MakerBogans/Fourbie/Fourbie v2/STL/XY Joints/v27 - Left XY Joint - Bottom.stl

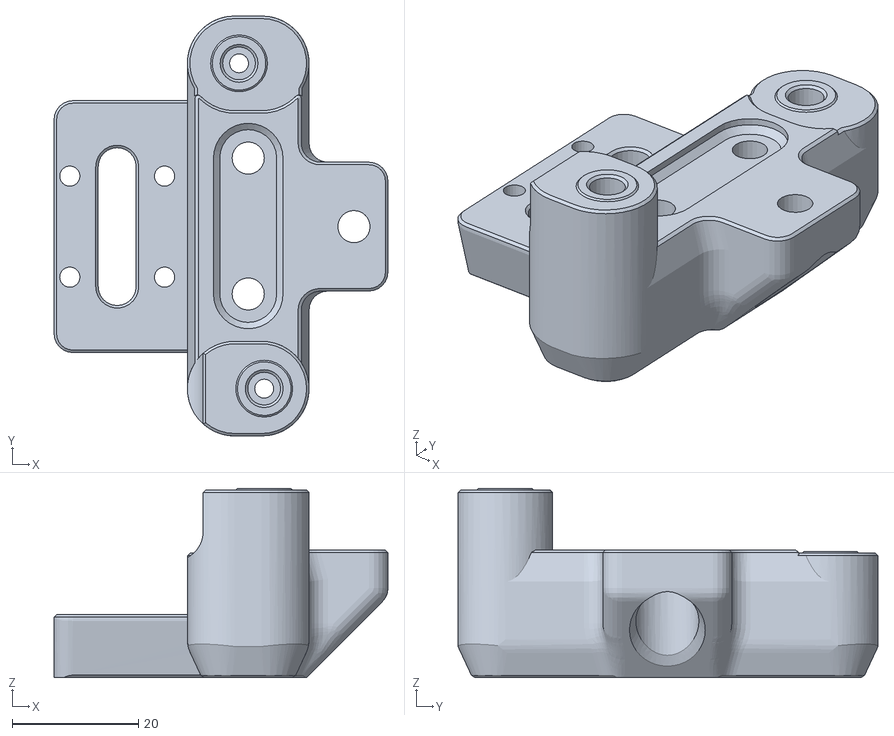
[picture p24: CAD file, 2023-07-19]
Fourbie v2/STL/XY Joints/v27 - Left XY Joint - Bottom.stl
52.9 x 66.5 x 30.0
