MakerBogans/Fourbie/Fourbie v2/Mods/Killajoedotcom/AB Drives for Trident/Front AB Drives/4 Inch Lift/Thicker Front Left_Fourbie v2_Tensioner Frame_x2.stl

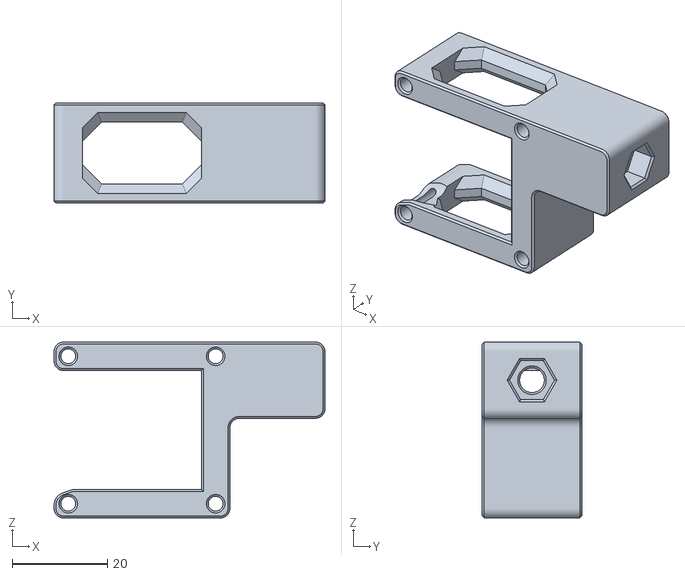
[picture p25: CAD file, 2024-02-14]
Fourbie v2/Mods/Killajoedotcom/AB Drives for Trident/Front AB Drives/4 Inch Lift/Thicker Front Left_Fourbie v2_Tensioner Frame_x2.stl
57.0 x 21.0 x 37.0
