MakerBogans/Fourbie/Fourbie v2/Mods/Killajoedotcom/AB Drives for Trident/Rear AB Drives/Rear AB - Right - Tensioner Frame.stl

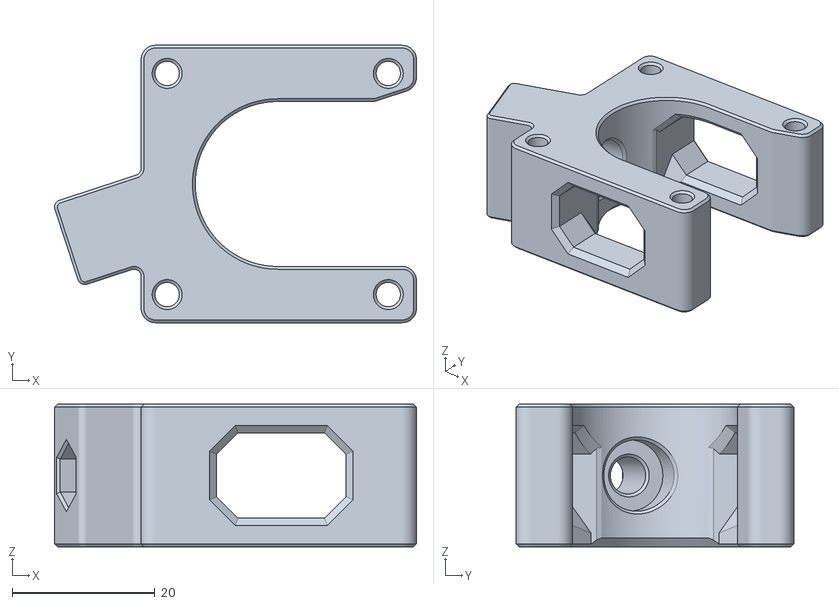
[picture p26: CAD file, 2024-02-14]
Fourbie v2/Mods/Killajoedotcom/AB Drives for Trident/Rear AB Drives/Rear AB - Right - Tensioner Frame.stl
50.7 x 38.9 x 20.0
