MakerBogans/Fourbie/Fourbie v2/Mods/Verethy/Eureaka Probe Dock/Goliath_short_wider_Eureka.3mf

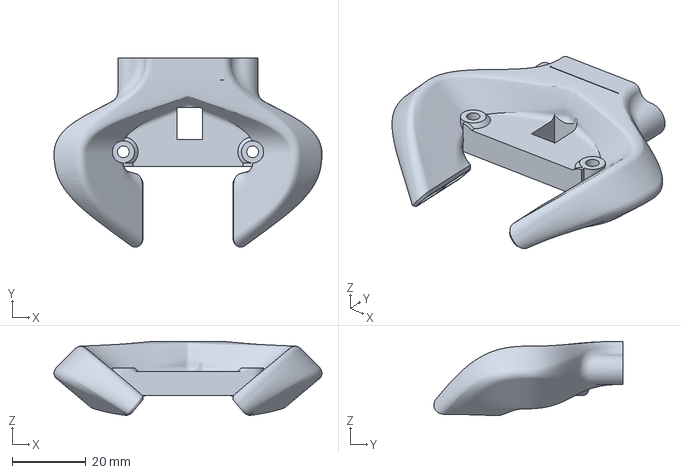
[picture p27: CAD file, 2023-07-19]
Fourbie v2/Mods/Verethy/Eureaka Probe Dock/Goliath_short_wider_Eureka.3mf
72.6 x 51.1 x 20.1 mm
