MakerBogans/Fourbie/Fourbie v2/STL/Cable Tie Mounts/Cable Tie Mount - Wider Base.stl

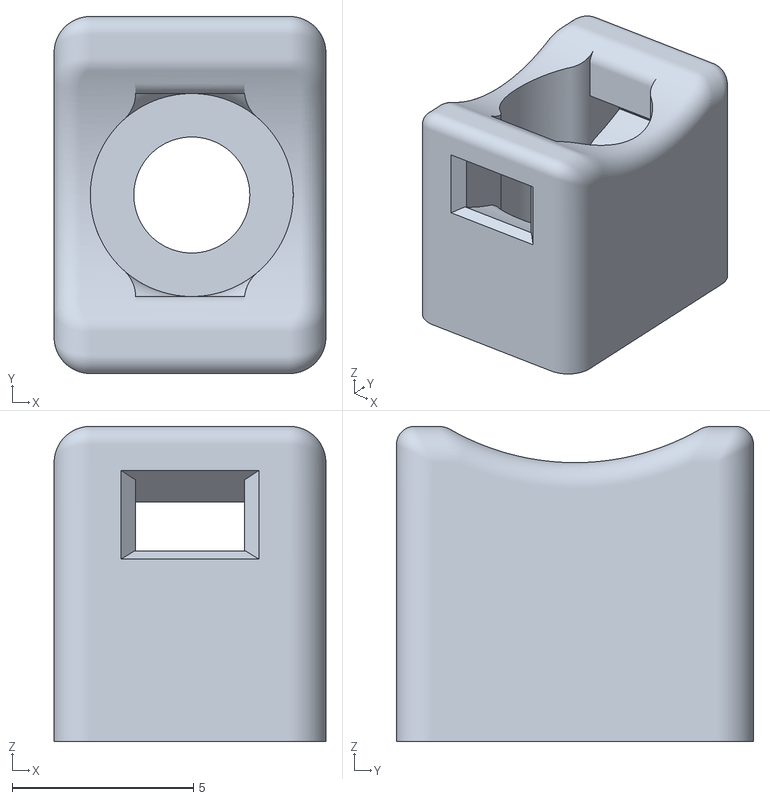
[picture p28: CAD file, 2023-06-04]
Fourbie v2/STL/Cable Tie Mounts/Cable Tie Mount - Wider Base.stl
7.50 x 9.85 x 8.70
