MakerBogans/Fourbie/Fourbie v2/STL/Toolhead/Alternative front belt clamps/Toothed Belt Clamp - Rear- x2 -Print Solid!.stl

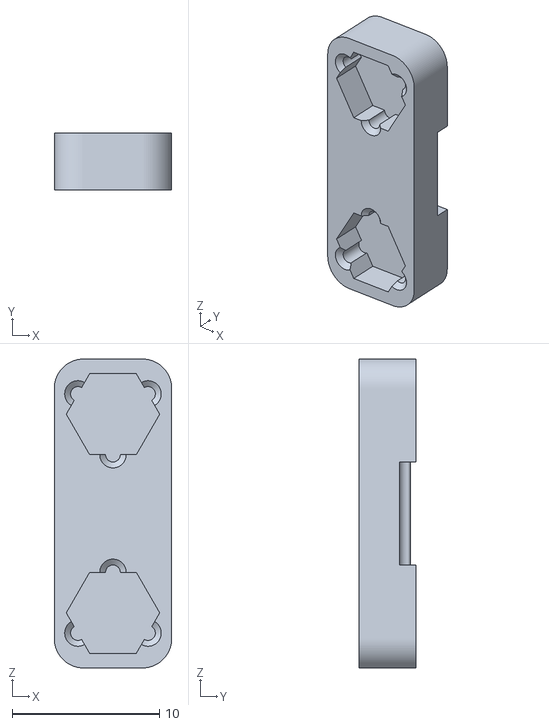
[picture p29: CAD file, 2023-06-04]
Fourbie v2/STL/Toolhead/Alternative front belt clamps/Toothed Belt Clamp - Rear- x2 -Print Solid!.stl
7.98 x 3.90 x 21.0
