MakerBogans/Fourbie/Fourbie v2/STL/Toolhead/VZBot Toolhead Mods/MGN9/Top plate MGN9H Sherpa Micro.stl

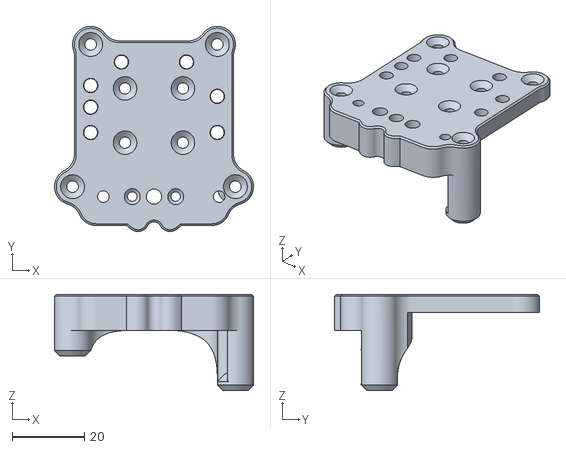
[picture p30: CAD file, 2023-06-04]
Fourbie v2/STL/Toolhead/VZBot Toolhead Mods/MGN9/Top plate MGN9H Sherpa Micro.stl
55.0 x 56.7 x 26.6
