MakerBogans/Fourbie/Fourbie v2/STL/Toolhead/VZBot Toolhead Mods/Stubby Back Plate - No Mast.stl

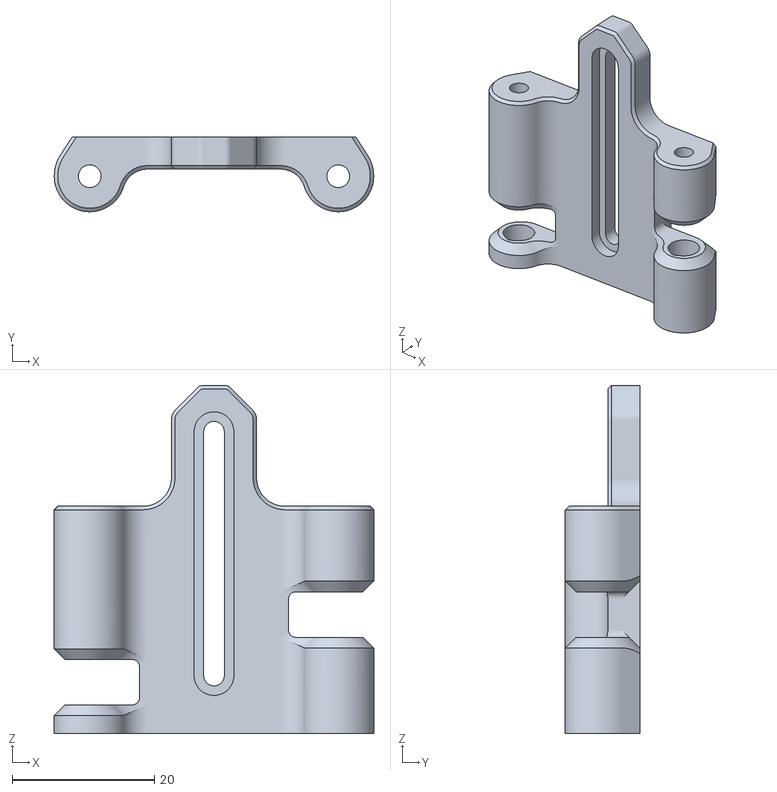
[picture p31: CAD file, 2023-06-04]
Fourbie v2/STL/Toolhead/VZBot Toolhead Mods/Stubby Back Plate - No Mast.stl
45.0 x 10.5 x 49.0
