MakerBogans/Fourbie/Fourbie v2/STL/Tools/CF Tube Drill Guild MGN12 End hole.stl

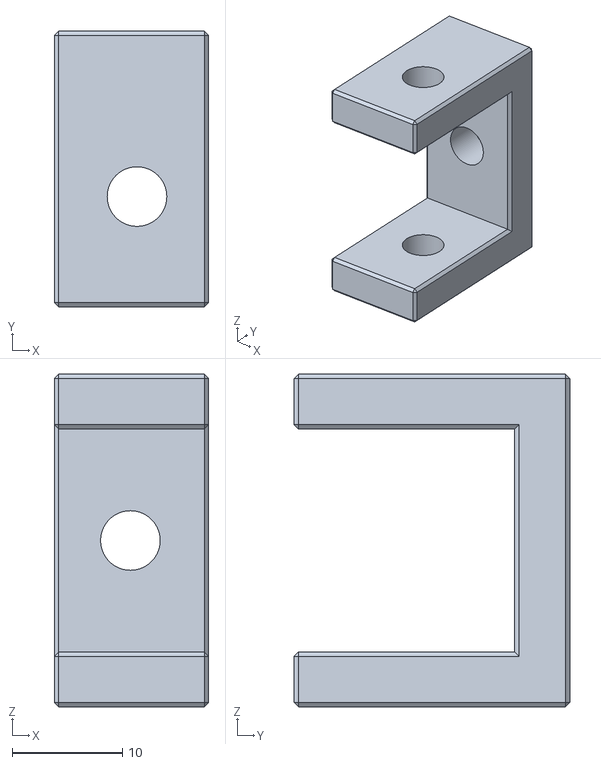
[picture p32: CAD file, 2023-06-04]
Fourbie v2/STL/Tools/CF Tube Drill Guild MGN12 End hole.stl
14.0 x 25.0 x 30.2
