MakerBogans/Fourbie/Fourbie v2/STL/XY Joints/MGN12/MGN12 XY Joints - Left - Bottom.stl

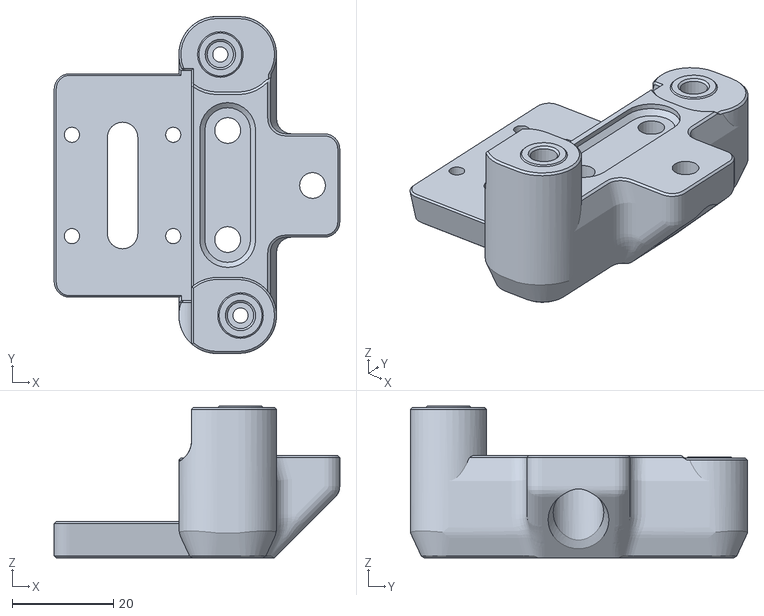
[picture p33: CAD file, 2023-07-19]
Fourbie v2/STL/XY Joints/MGN12/MGN12 XY Joints - Left - Bottom.stl
56.4 x 66.5 x 30.0
