MakerBogans/Fourbie/Fourbie v2/Mods/Killajoedotcom/AB Drives for Trident/Front AB Drives/4 Inch Lift/Thicker Front Left_Fourbie v2_Top.stl

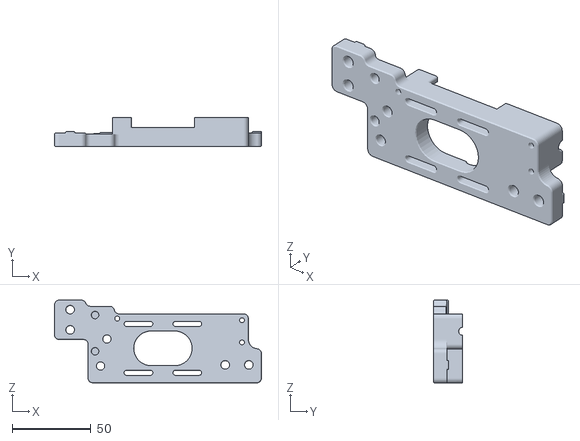
[picture p35: CAD file, 2024-02-14]
Fourbie v2/Mods/Killajoedotcom/AB Drives for Trident/Front AB Drives/4 Inch Lift/Thicker Front Left_Fourbie v2_Top.stl
131.4 x 18.6 x 52.5
