MakerBogans/Fourbie/Fourbie v2/Mods/Killajoedotcom/AB Drives for Trident/Front AB Drives/Knurled Knob_x2.3mf

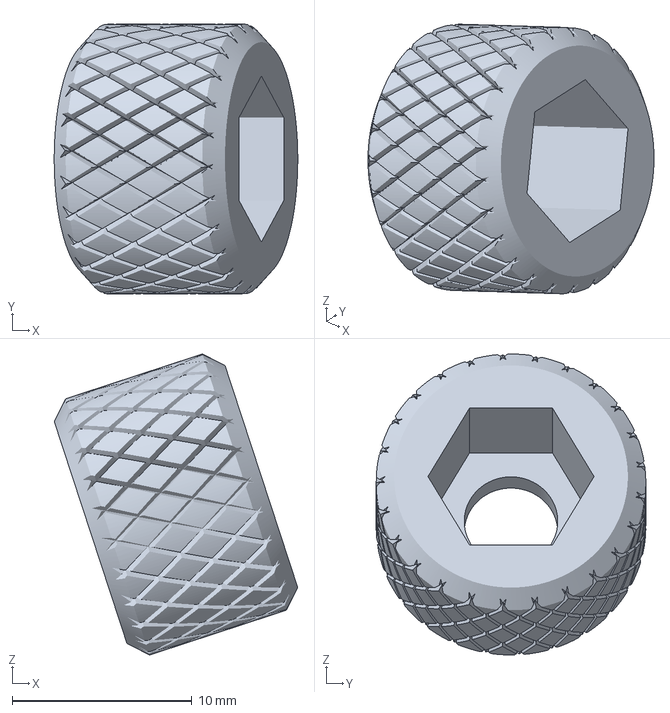
[picture p36: CAD file, 2024-02-14]
Fourbie v2/Mods/Killajoedotcom/AB Drives for Trident/Front AB Drives/Knurled Knob_x2.3mf
13.6 x 15.0 x 16.7 mm
