MakerBogans/Fourbie/Fourbie v2/STL/AB/v26 - Rear Right - Bottom.stl

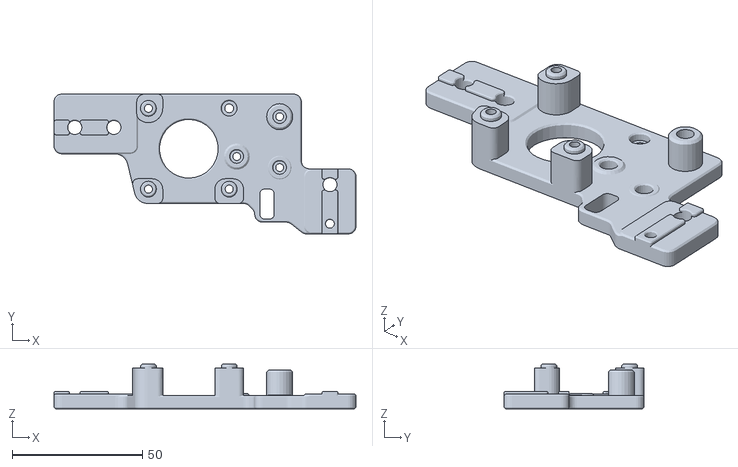
[picture p37: CAD file, 2023-07-19]
Fourbie v2/STL/AB/v26 - Rear Right - Bottom.stl
115.9 x 53.7 x 17.1
