MakerBogans/Fourbie/Fourbie v2/STL/Cable Tie Mounts/Cable Tie Mount - Flat top wide base.stl

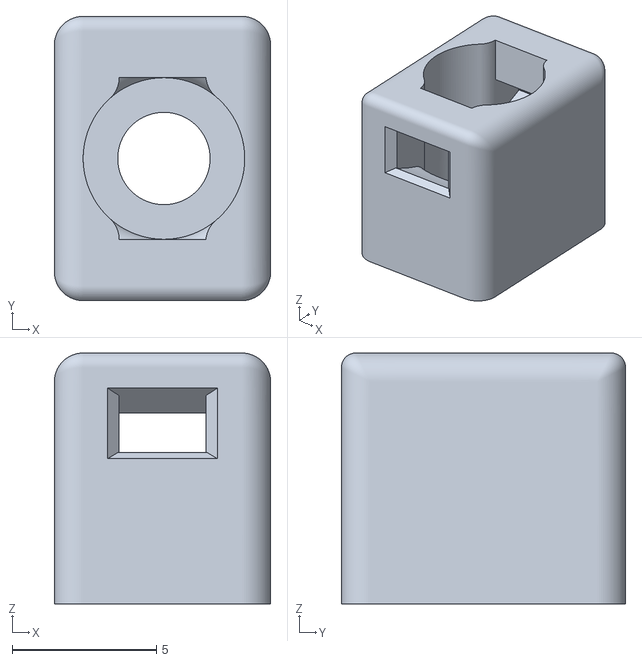
[picture p38: CAD file, 2023-06-04]
Fourbie v2/STL/Cable Tie Mounts/Cable Tie Mount - Flat top wide base.stl
7.50 x 9.85 x 8.70
