MakerBogans/Fourbie/Fourbie v2/STL/Toolhead/VZBot Toolhead Mods/LGX Lite Side Cable Holder.stl

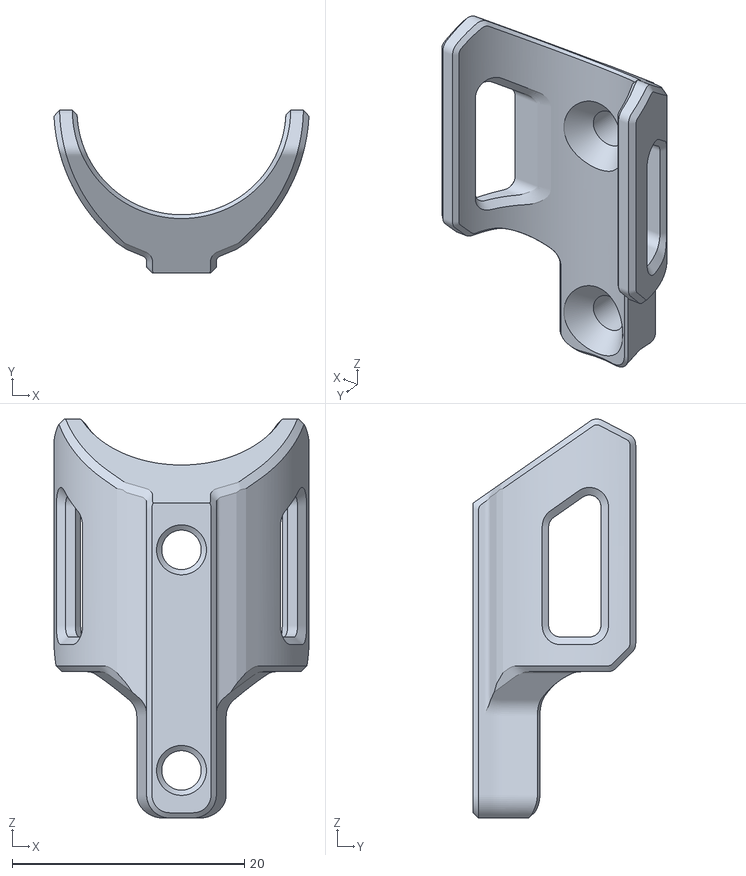
[picture p39: CAD file, 2023-06-04]
Fourbie v2/STL/Toolhead/VZBot Toolhead Mods/LGX Lite Side Cable Holder.stl
22.0 x 14.0 x 34.4
