MakerBogans/Fourbie/Fourbie v2/STL/Tools/CF Tube Drill Guide MGN9 Rail Retainer.stl

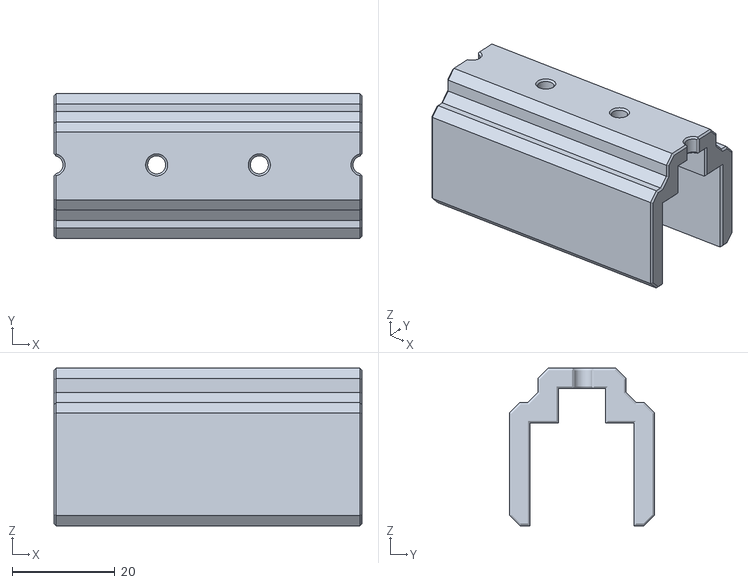
[picture p40: CAD file, 2023-06-04]
Fourbie v2/STL/Tools/CF Tube Drill Guide MGN9 Rail Retainer.stl
60.0 x 28.2 x 30.7
