MakerBogans/Fourbie/Fourbie v2/STL/XY Joints/MGN12/MGN12 XY Joints - Right - Top.stl

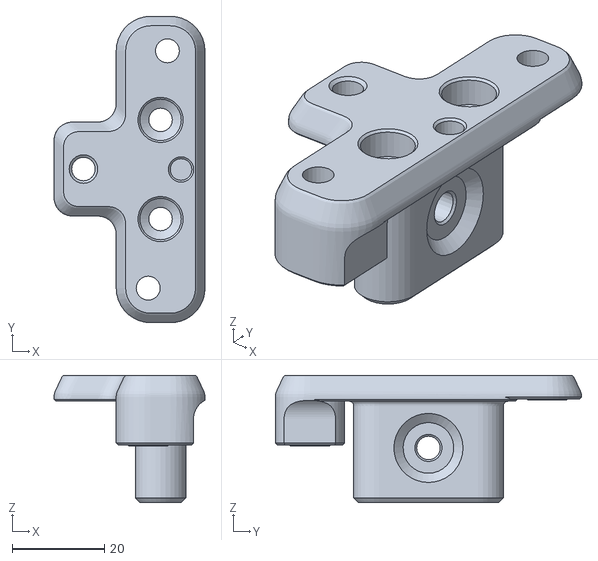
[picture p41: CAD file, 2023-07-19]
Fourbie v2/STL/XY Joints/MGN12/MGN12 XY Joints - Right - Top.stl
32.8 x 66.5 x 27.6
