MakerBogans/Fourbie/Fourbie v2/Mods/Killajoedotcom/AB Drives for Trident/Front AB Drives/Front AB - Right - Top.3mf

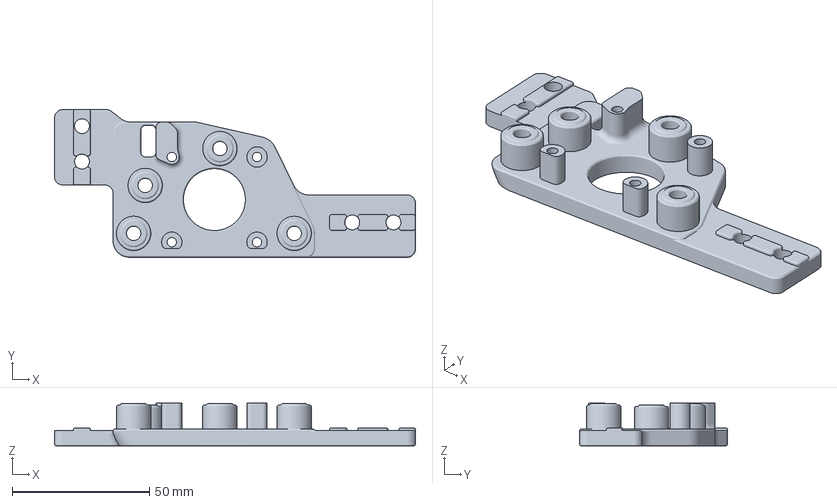
[picture p43: CAD file, 2024-02-14]
Fourbie v2/Mods/Killajoedotcom/AB Drives for Trident/Front AB Drives/Front AB - Right - Top.3mf
131.3 x 53.7 x 15.6 mm
