MakerBogans/Fourbie/Fourbie v2/Mods/Killajoedotcom/AB Drives for Trident/Rear AB Drives/Knob - Basic.stl

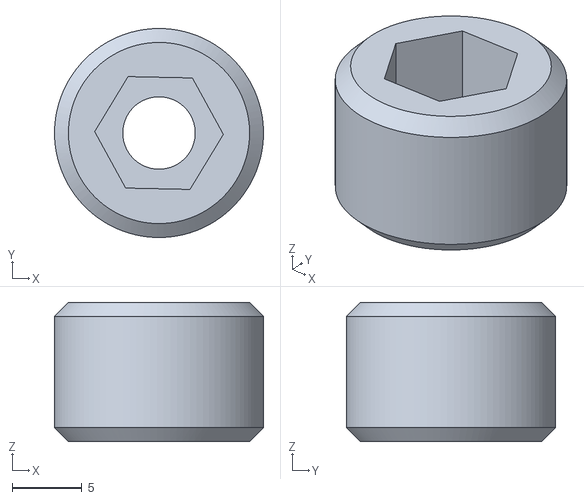
[picture p44: CAD file, 2024-02-14]
Fourbie v2/Mods/Killajoedotcom/AB Drives for Trident/Rear AB Drives/Knob - Basic.stl
15.0 x 15.0 x 10.0
