MakerBogans/Fourbie/Fourbie v2/STL/AB/v26 - Front Right - Top.stl

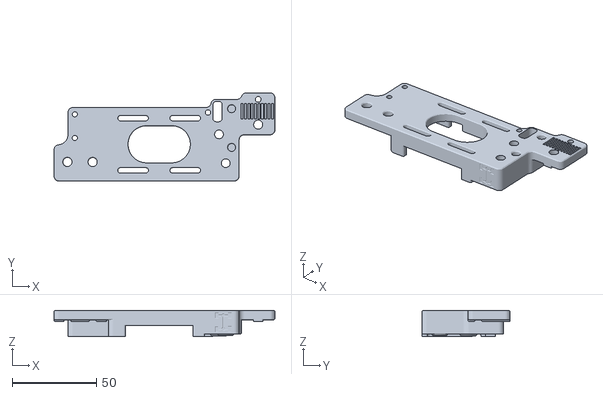
[picture p45: CAD file, 2023-07-19]
Fourbie v2/STL/AB/v26 - Front Right - Top.stl
131.4 x 52.5 x 15.6
