MakerBogans/Fourbie/Fourbie v2/STL/Cable Tie Mounts/Cable Tie Mount.stl

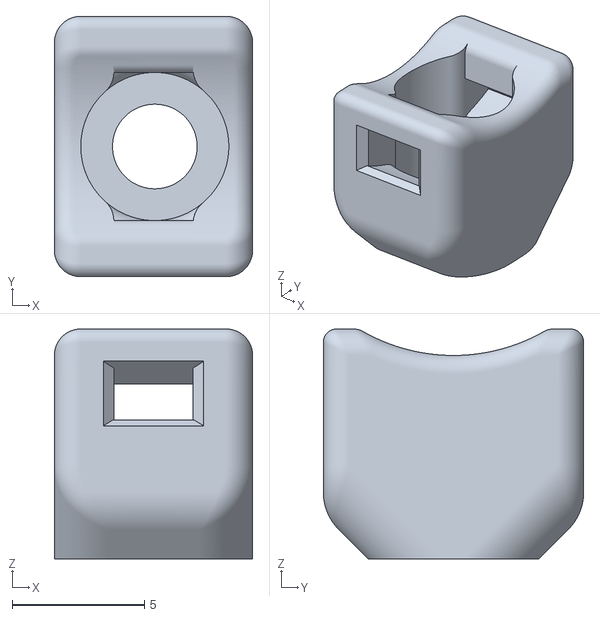
[picture p46: CAD file, 2023-06-04]
Fourbie v2/STL/Cable Tie Mounts/Cable Tie Mount.stl
7.50 x 9.85 x 8.70
