MakerBogans/Fourbie/Fourbie v2/STL/Toolhead/VZBot Toolhead Mods/Stubby 5015 back sliding mount - no mast.stl

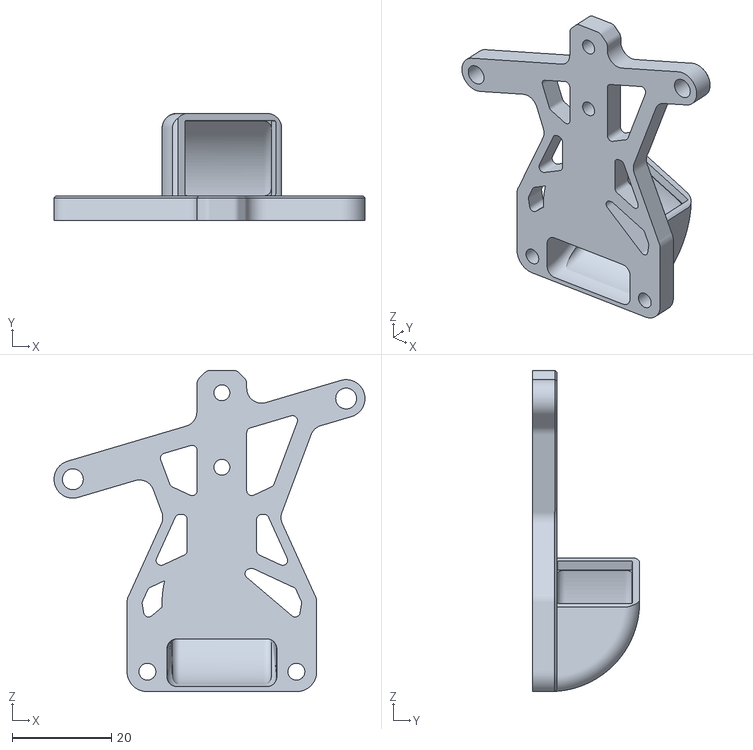
[picture p47: CAD file, 2023-06-04]
Fourbie v2/STL/Toolhead/VZBot Toolhead Mods/Stubby 5015 back sliding mount - no mast.stl
62.6 x 21.6 x 64.7
