MakerBogans/Fourbie/Fourbie v2/STL/XY Joints/Tube End 18mm ID x2.stl

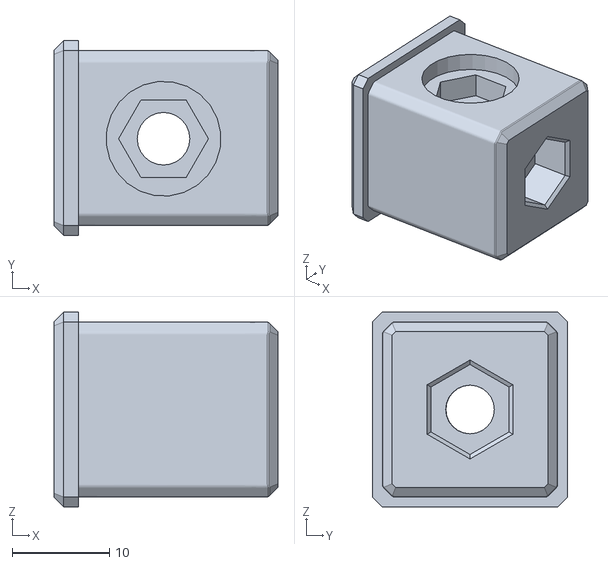
[picture p49: CAD file, 2023-07-19]
Fourbie v2/STL/XY Joints/Tube End 18mm ID x2.stl
23.0 x 20.0 x 20.0
