MakerBogans/Fourbie/Fourbie v2/Mods/Killajoedotcom/AB Drives for Trident/Rear AB Drives/Knob - Flanged.stl

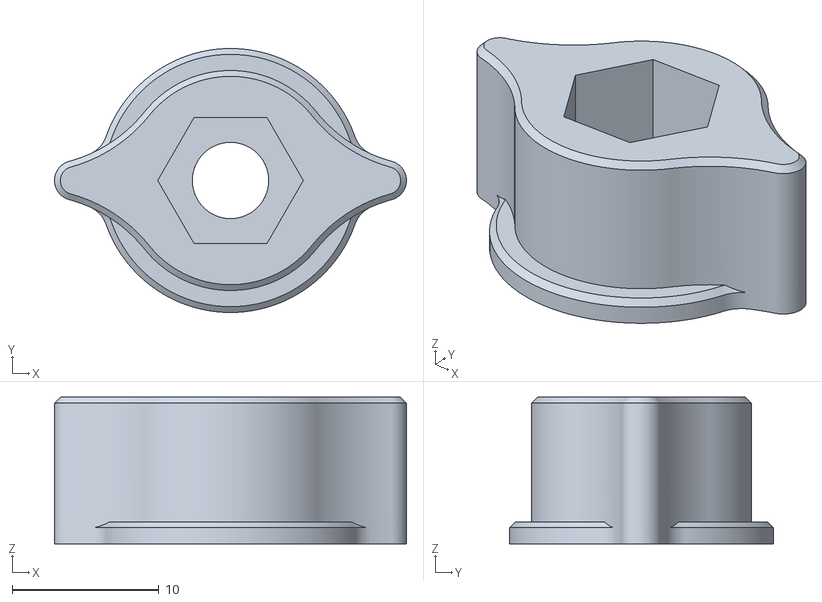
[picture p50: CAD file, 2024-02-14]
Fourbie v2/Mods/Killajoedotcom/AB Drives for Trident/Rear AB Drives/Knob - Flanged.stl
24.0 x 18.0 x 10.0
