MakerBogans/Fourbie/Fourbie v2/STL/XY Joints/X Endstop.stl

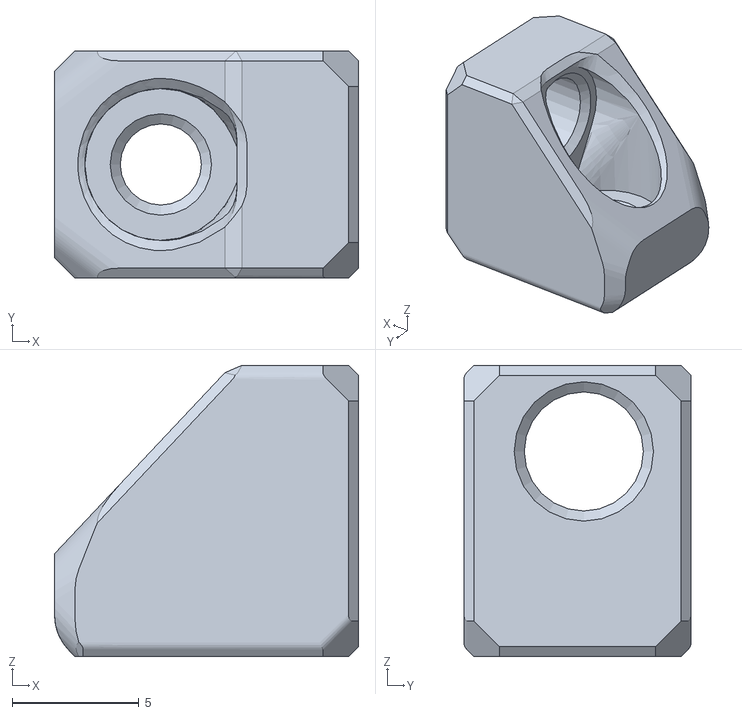
[picture p51: CAD file, 2023-07-19]
Fourbie v2/STL/XY Joints/X Endstop.stl
12.0 x 8.97 x 11.5
