MakerBogans/Fourbie/Fourbie v2/STL/XY Joints/v27 - Right XY Joint - Top.stl

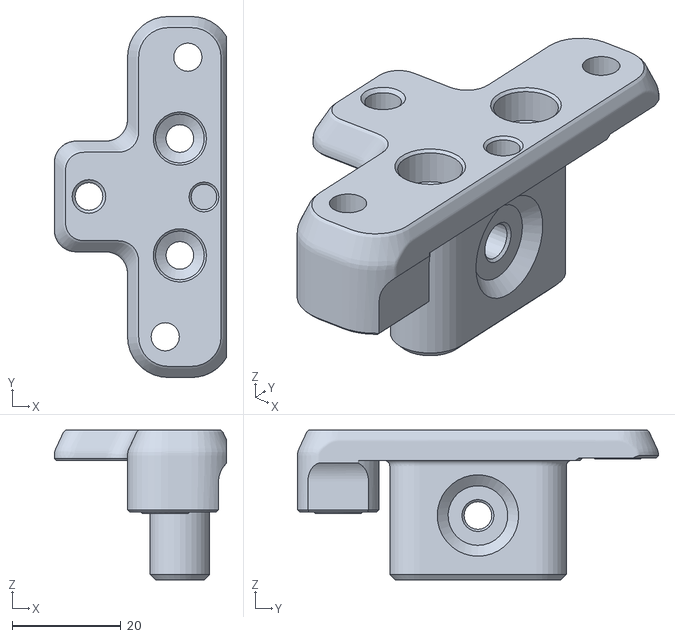
[picture p54: CAD file, 2023-07-19]
Fourbie v2/STL/XY Joints/v27 - Right XY Joint - Top.stl
31.8 x 66.5 x 27.6
