MakerBogans/Fourbie/Fourbie v2/STL/AB/v26 - Front Right - Bottom.stl

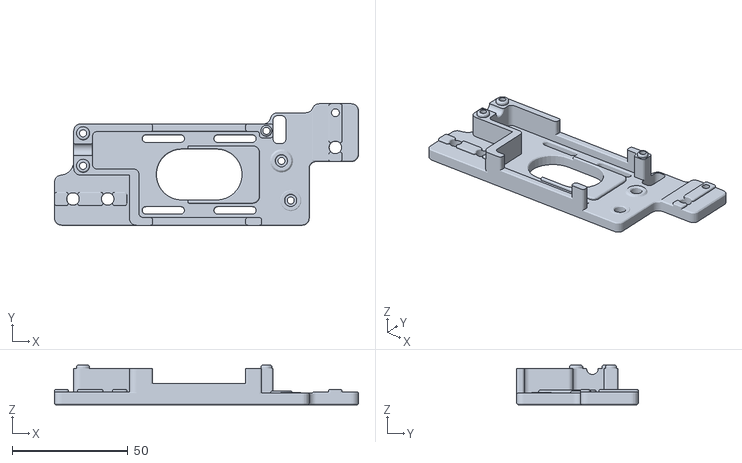
[picture p55: CAD file, 2023-07-19]
Fourbie v2/STL/AB/v26 - Front Right - Bottom.stl
131.4 x 52.5 x 17.1
