MakerBogans/Fourbie/Fourbie v2/STL/AB/v26 - Front Left - Bottom.stl

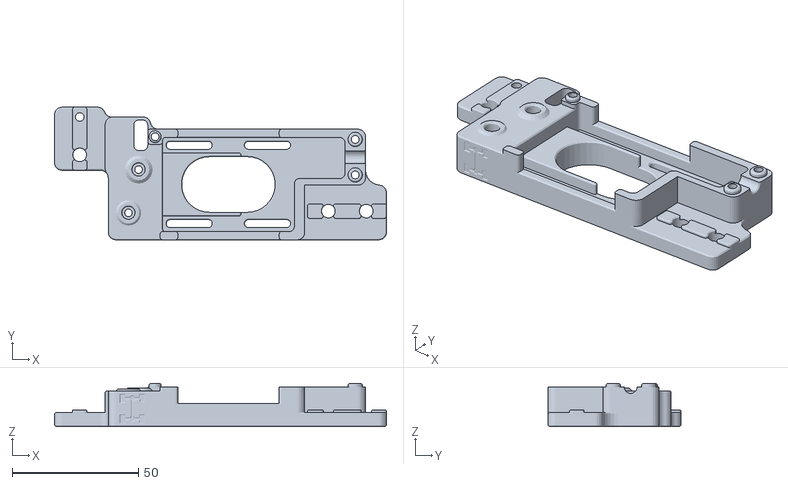
[picture p56: CAD file, 2023-07-19]
Fourbie v2/STL/AB/v26 - Front Left - Bottom.stl
131.4 x 52.5 x 17.1
