MakerBogans/Fourbie/Fourbie v2/STL/AB/Front Lef - Y Endstop.stl

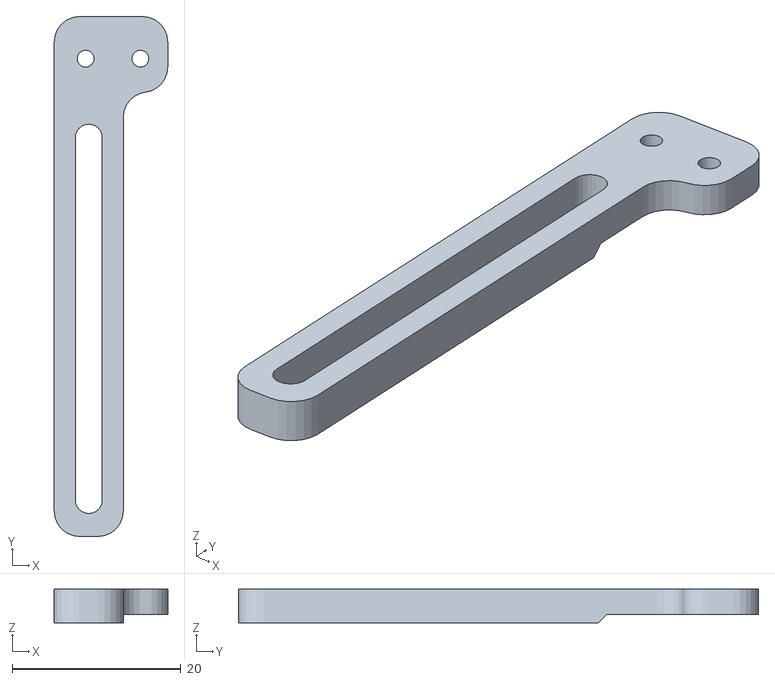
[picture p57: CAD file, 2023-07-19]
Fourbie v2/STL/AB/Front Lef - Y Endstop.stl
13.5 x 61.7 x 4.00
